opendata-heilbronn/MateLight/docs/img/contributors/Franz.jpg

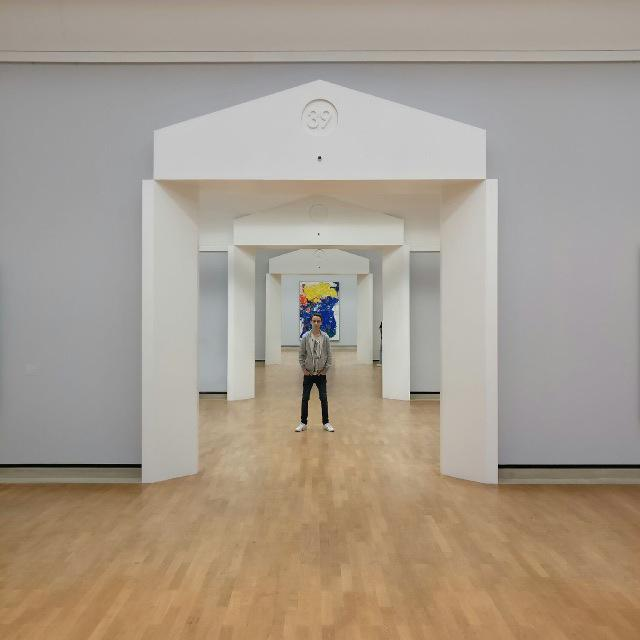
docs/img/contributors/Franz.jpg
