opendata-heilbronn/MateLight/docs/img/contributors/harmoniemand.jpg

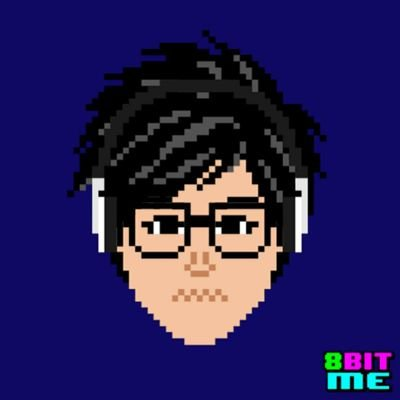
docs/img/contributors/harmoniemand.jpg
