opendata-heilbronn/MateLight/docs/img/contributors/theVale98.jpg

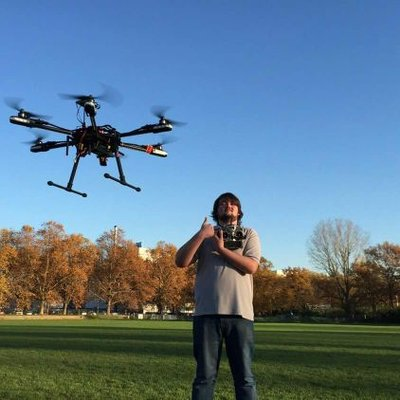
docs/img/contributors/theVale98.jpg
