opendata-heilbronn/MateLight/Raspberry_Pi/gLEDiator/gifs/Karate_Dancing.gif

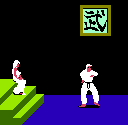
Raspberry_Pi/gLEDiator/gifs/Karate_Dancing.gif
